MilosRasic98/ClaudeMonitorCompanion/Code/include/customface.h

#pragma once
#include <stddef.h>
#include <stdint.h>

// A face the user draws themselves, on the settings page.
//
// 24 x 28 cells at 10 screen pixels each is exactly 240 x 280, so the grid maps
// one-to-one onto the panel with no scaling and no rounding.
//
// Two frames per face: resting and blink. If the blink frame is empty the board
// simply does not blink.
//
// Everything else the built-in faces do — the working sweep, the bored droop,
// the excited bounce, the poke shake — comes from *translating* the drawing
// within the panel and letting the background fill what the shift vacates. The
// parametric faces animate by changing shape; a bitmap cannot, but it can move,
// and moving turns out to carry most of the expression. So a drawn face gets
// the same mood vocabulary as a built-in one without the user drawing a single
// extra frame.
//
// Offsets are whole cells. The art is ten-pixel blocks, so moving in ten-pixel
// steps is what keeps it looking like the same object rather than a bitmap
// sliding around underneath a grid.
//
// Four slots, so a few faces can be drawn and swiped between. Only slots that
// actually hold a drawing join the rotation; empty ones would be dead screens.

namespace customface {

const int kW = 24;
const int kH = 28;
const int kCell = 10;
const int kCells = kW * kH;              // 672
const int kFrameBytes = kCells / 4;      // 2 bits per cell -> 168
const int kSlotBytes = kFrameBytes * 2;  // 336 per face
const int kSlots = 4;

enum Ink : uint8_t { kBg = 0, kInk = 1, kLit = 2 };

void begin();

// Raw bytes for one slot: frame 0 then frame 1, row-major, four cells per byte,
// most significant bits first. Returns false on a bad slot or wrong length.
bool store(int slot, const uint8_t *data, size_t len);
const uint8_t *data(int slot);

bool has_drawing(int slot);  // frame 0 has any non-background cell
bool has_blink(int slot);    // frame 1 does too, so blinking is worth doing
bool any_drawing();
int used_count();

// Paint a frame, translated by whole cells. Only cells that differ from what is
// currently on screen are drawn, so a blink or a one-cell drift costs a handful
// of rectangles rather than 672.
void draw(int slot, int frame, uint16_t bg, int dx_cells, int dy_cells);

// Forget what is on screen. Call after anything else has painted over the face
// — a full repaint, a style change — so the next draw() does not skip cells it
// believes are already correct.
void invalidate();

}  // namespace customface
