MilosRasic98/ClaudeMonitorCompanion/Code/src/ui/customface.cpp

#include "customface.h"

#include <Arduino.h>
#include <Preferences.h>
#include <string.h>

#include "display.h"
#include "pins.h"
#include "tuning.h"

namespace customface {
namespace {

Preferences s_prefs;
uint8_t s_data[kSlots][kSlotBytes];

bool valid(int slot) { return slot >= 0 && slot < kSlots; }

// What is currently on the panel, one ink value per cell. Diffing against this
// rather than against the other frame means the same cheap path serves a blink,
// a drift, a bounce and a slot change alike.
uint8_t s_shown[kCells];
bool s_shown_valid = false;

// Four cells per byte, most significant bits first.
inline uint8_t cell_at(int slot, int frame, int i) {
  const int idx = frame * kFrameBytes + (i >> 2);
  const int shift = 6 - 2 * (i & 3);
  return (uint8_t)((s_data[slot][idx] >> shift) & 0x3);
}

uint16_t colour_of(uint8_t v, uint16_t bg) {
  switch (v) {
    case kInk: return kBlack;
    case kLit: return kWhite;
    default:   return bg;
  }
}

bool frame_used(int slot, int frame) {
  const uint8_t *p = s_data[slot] + frame * kFrameBytes;
  for (int i = 0; i < kFrameBytes; i++) {
    if (p[i]) return true;
  }
  return false;
}

}  // namespace

void begin() {
  s_prefs.begin("face", false);
  memset(s_data, 0, sizeof(s_data));
  // One NVS key per slot, so saving one face does not rewrite the others.
  for (int i = 0; i < kSlots; i++) {
    char k[8];
    snprintf(k, sizeof(k), "bmp%d", i);
    s_prefs.getBytes(k, s_data[i], kSlotBytes);
  }
}

bool store(int slot, const uint8_t *in, size_t len) {
  if (!valid(slot) || len != (size_t)kSlotBytes) return false;
  memcpy(s_data[slot], in, kSlotBytes);
  char k[8];
  snprintf(k, sizeof(k), "bmp%d", slot);
  s_prefs.putBytes(k, s_data[slot], kSlotBytes);
  return true;
}

const uint8_t *data(int slot) { return s_data[valid(slot) ? slot : 0]; }
bool has_drawing(int slot) { return valid(slot) && frame_used(slot, 0); }
bool has_blink(int slot) { return valid(slot) && frame_used(slot, 1); }

bool any_drawing() {
  for (int i = 0; i < kSlots; i++) {
    if (has_drawing(i)) return true;
  }
  return false;
}

int used_count() {
  int n = 0;
  for (int i = 0; i < kSlots; i++) {
    if (has_drawing(i)) n++;
  }
  return n;
}

void invalidate() { s_shown_valid = false; }

void draw(int slot, int frame, uint16_t bg, int dx, int dy) {
  if (!valid(slot)) return;

  for (int row = 0; row < kH; row++) {
    int run_start = -1;
    uint16_t run_c = 0;

    // One past the right edge so a run reaching the edge still gets flushed.
    for (int col = 0; col <= kW; col++) {
      bool want = false;
      uint16_t c = 0;

      if (col < kW) {
        // Sample the drawing shifted by (dx, dy). Anything the shift moves in
        // from outside is background, which is what makes the face look like it
        // moved rather than wrapped.
        const int sx = col - dx, sy = row - dy;
        const uint8_t v = (sx >= 0 && sx < kW && sy >= 0 && sy < kH)
                              ? cell_at(slot, frame, sy * kW + sx)
                              : kBg;
        const int i = row * kW + col;
        if (!s_shown_valid || v != s_shown[i]) {
          c = colour_of(v, bg);
          want = true;
        }
        s_shown[i] = v;
      }

      if (run_start >= 0 && (!want || c != run_c)) {
        display::fill_rect(run_start * kCell, row * kCell,
                           (col - run_start) * kCell, kCell, run_c);
        run_start = -1;
      }
      if (want && run_start < 0) {
        run_start = col;
        run_c = c;
      }
    }
  }
  s_shown_valid = true;
}

}  // namespace customface
